shodelta/Megapede/Body/stl/MP_Heart_x1.stl

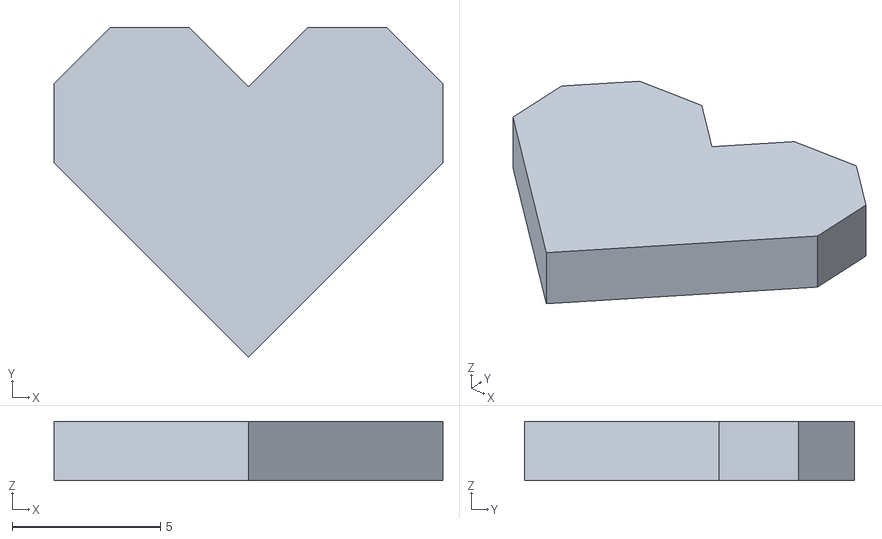
[picture p18: CAD file, 2015-07-23]
Body/stl/MP_Heart_x1.stl
13.1 x 11.1 x 2.00
