shodelta/Megapede/Body/stl/MP_Bridge_x4.stl

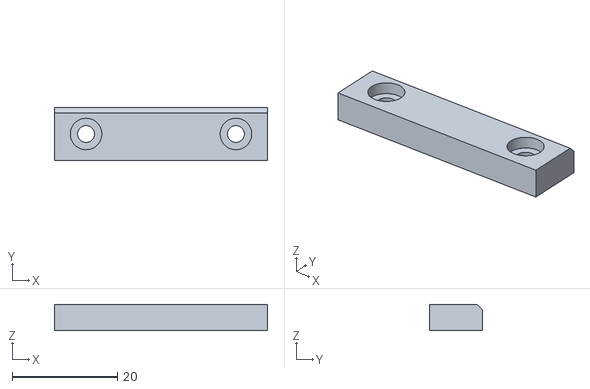
[picture p19: CAD file, 2015-07-23]
Body/stl/MP_Bridge_x4.stl
40.5 x 10.0 x 5.00
