shodelta/Megapede/Body/stl/MP_Cring_x76.stl

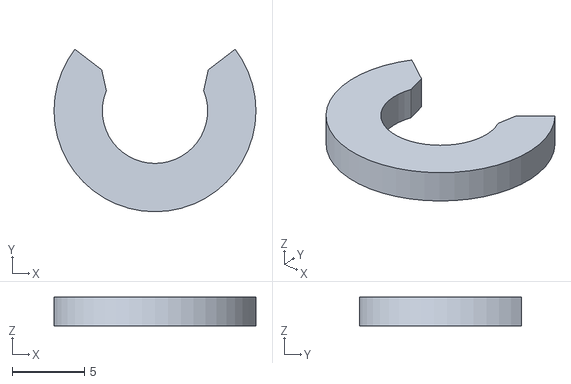
[picture p20: CAD file, 2015-07-23]
Body/stl/MP_Cring_x76.stl
14.0 x 11.3 x 2.00
